Zubax/gridsens_gs2/firmware/src/air_sensor.cpp

/*
 * Copyright (C) 2014-2015  Zubax Robotics  <info@zubax.com>
 *
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
 * Author: Pavel Kirienko <pavel.kirienko@zubax.com>
 */

#include "air_sensor.hpp"
#include "node.hpp"
#include "board/ms5611.hpp"

#include <uavcan/equipment/air_data/StaticPressure.hpp>
#include <uavcan/equipment/air_data/StaticTemperature.hpp>

#include <ch.hpp>
#include <zubax_chibios/os.hpp>
#include <zubax_chibios/util/helpers.hpp>
#include <unistd.h>


namespace air_sensor
{
namespace
{

constexpr unsigned TemperaturePeriodRatio = 5;

const float OperatingTemperatureRange[] = {             ///< Operating temperature, defined by the specification
    -40 + ms5611::DegreesCelsiusToKelvinOffset,
    +80 + ms5611::DegreesCelsiusToKelvinOffset
};

const unsigned MinPublicationPeriodUSec = unsigned(1e6 / 40);

os::config::Param<unsigned> param_period_usec("uavcan.pubp-pres",
                                              0, 0, 1000000);

os::config::Param<unsigned> param_prio("uavcan.prio-pres",
                                       16,
                                       uavcan::TransferPriority::NumericallyMin,
                                       uavcan::TransferPriority::NumericallyMax);

os::config::Param<float> param_pressure_variance("pres.variance", 100.0, 1.0, 4000.0);
os::config::Param<float> param_temperature_variance("temp.variance", 4.0, 1.0, 100.0);

chibios_rt::Mutex last_sample_mutex;
Sample last_sample;


class AirSensorThread : public chibios_rt::BaseStaticThread<1024>
{
    float pressure_variance = 0;
    float temperature_variance = 0;

    mutable os::watchdog::Timer watchdog_;
    mutable ms5611::MS5611 driver_;

    static bool isInRange(float value, const float range_min_max[2])
    {
        return (value >= range_min_max[0]) && (value <= range_min_max[1]);
    }

    void publish(float pressure_pa, float temperature_k) const
    {
        {
            os::MutexLocker mlock(last_sample_mutex);
            last_sample.seq_id++;
            last_sample.pressure_pa = pressure_pa;
            last_sample.temperature_k = temperature_k;
        }

        if (!node::isStarted())
        {
            return;
        }

        static uavcan::equipment::air_data::StaticPressure pressure;
        pressure.static_pressure = pressure_pa;
        pressure.static_pressure_variance = pressure_variance;

        static uavcan::equipment::air_data::StaticTemperature temperature;
        temperature.static_temperature = temperature_k;
        temperature.static_temperature_variance = temperature_variance;

        node::Lock locker;
        auto& node = node::getNode();

        static uavcan::Publisher<uavcan::equipment::air_data::StaticPressure> pressure_pub(node);
        static uavcan::Publisher<uavcan::equipment::air_data::StaticTemperature> temperature_pub(node);

        EXECUTE_ONCE_NON_THREAD_SAFE
        {
            pressure_pub.setPriority(param_prio.get());
            temperature_pub.setPriority(param_prio.get());
        }

        (void)pressure_pub.broadcast(pressure);

        static unsigned temperature_publishing_frequency_divider = 0;
        temperature_publishing_frequency_divider++;
        if (temperature_publishing_frequency_divider >= TemperaturePeriodRatio)
        {
            temperature_publishing_frequency_divider = 0;
            (void)temperature_pub.broadcast(temperature);
        }
    }

    void tryRun() const
    {
        systime_t sleep_until = chibios_rt::System::getTime();

        assert(param_period_usec.get() > 0);
        const unsigned period_usec = std::max(MinPublicationPeriodUSec, param_period_usec.get());

        while (!os::isRebootRequested())
        {
            watchdog_.reset();
            sleep_until += US2ST(period_usec);

            const auto sample = driver_.read();
            if (!sample.first)
            {
                os::lowsyslog("Air sensor read failed\n");
                break;
            }

            publish(sample.second.pressure, sample.second.temperature);

            if (!isInRange(sample.second.temperature, OperatingTemperatureRange))
            {
                node::setComponentHealth(node::ComponentID::AirSensor, uavcan::protocol::NodeStatus::HEALTH_WARNING);
            }
            else
            {
                node::setComponentHealth(node::ComponentID::AirSensor, uavcan::protocol::NodeStatus::HEALTH_OK);
            }

            os::sleepUntilChTime(sleep_until);
        }
    }

public:
    AirSensorThread() :
        driver_(&SPID3, GPIO_PORT_BAROMETER_CHIP_SELECT, GPIO_PIN_BAROMETER_CHIP_SELECT)
    { }

    virtual ~AirSensorThread() { }

    void main() override
    {
        watchdog_.startMSec(1100);
        setName("air_sensor");

        pressure_variance = param_pressure_variance.get();
        temperature_variance = param_temperature_variance.get();

        while (!os::isRebootRequested())
        {
            watchdog_.reset();
            ::usleep(500000);
            watchdog_.reset();

            if (!driver_.init())
            {
                os::lowsyslog("Air sensor init failed, will retry...\n");
                continue;
            }

            os::lowsyslog("Air sensor init OK\n");

            node::markComponentInitialized(node::ComponentID::AirSensor);
            tryRun();
            if (!os::isRebootRequested())
            {
                node::setComponentHealth(node::ComponentID::AirSensor, uavcan::protocol::NodeStatus::HEALTH_ERROR);
                os::lowsyslog("Air sensor is about to restart...\n");
            }
        }

        os::lowsyslog("Air sensor driver terminated\n");
    }
} air_sensor_thread;

}

void init()
{
    if (param_period_usec.get() > 0)
    {
        (void)air_sensor_thread.start(HIGHPRIO - 10);
    }
    else
    {
        node::markComponentInitialized(node::ComponentID::AirSensor);
        os::lowsyslog("Air sensor disabled\n");
    }
}

Sample getLastSample()
{
    os::MutexLocker mlock(last_sample_mutex);
    return last_sample;
}

}
