Zubax/gridsens_gs2/firmware/src/sys/mcuconf.h

/*
 * STM32F107 drivers configuration.
 * The following settings override the default settings present in
 * the various device driver implementation headers.
 * Note that the settings for each driver only have effect if the whole
 * driver is enabled in halconf.h.
 *
 * IRQ priorities:
 * 15...0       Lowest...Highest.
 *
 * DMA priorities:
 * 0...3        Lowest...Highest.
 */

#define STM32F107_MCUCONF

#define STM32_ST_USE_TIMER                  5

/*
 * HAL driver system settings.
 */
#define STM32_NO_INIT                       FALSE
#define STM32_HSI_ENABLED                   TRUE  // Needed for FLASH programming
#define STM32_LSI_ENABLED                   TRUE  // Needed for watchdog
#define STM32_HSE_ENABLED                   TRUE
#define STM32_LSE_ENABLED                   FALSE
#define STM32_SW                            STM32_SW_PLL
#define STM32_PLLSRC                        STM32_PLLSRC_PREDIV1
#define STM32_PREDIV1SRC                    STM32_PREDIV1SRC_HSE
#define STM32_PREDIV1_VALUE                 2
#define STM32_PLLMUL_VALUE                  9
#define STM32_PREDIV2_VALUE                 4
#define STM32_PLL2MUL_VALUE                 16
#define STM32_PLL3MUL_VALUE                 16
#define STM32_HPRE                          STM32_HPRE_DIV1
#define STM32_PPRE1                         STM32_PPRE1_DIV2
#define STM32_PPRE2                         STM32_PPRE2_DIV2
#define STM32_ADCPRE                        STM32_ADCPRE_DIV4
#define STM32_OTG_CLOCK_REQUIRED            TRUE
#define STM32_OTGFSPRE                      STM32_OTGFSPRE_DIV3
#define STM32_I2S_CLOCK_REQUIRED            FALSE
#define STM32_MCOSEL                        STM32_MCOSEL_NOCLOCK
#define STM32_RTCSEL                        STM32_RTCSEL_HSEDIV
#define STM32_PVD_ENABLE                    FALSE
#define STM32_PLS                           STM32_PLS_LEV0

/*
 * ADC driver system settings.
 */
#define STM32_ADC_USE_ADC1                  FALSE
#define STM32_ADC_ADC1_DMA_PRIORITY         2
#define STM32_ADC_ADC1_IRQ_PRIORITY         6

/*
 * CAN driver system settings.
 */
#define STM32_CAN_USE_CAN1                  FALSE
#define STM32_CAN_USE_CAN2                  FALSE
#define STM32_CAN_CAN1_IRQ_PRIORITY         4
#define STM32_CAN_CAN2_IRQ_PRIORITY         4

/*
 * EXT driver system settings.
 */
#define STM32_EXT_EXTI0_IRQ_PRIORITY        6
#define STM32_EXT_EXTI1_IRQ_PRIORITY        6
#define STM32_EXT_EXTI2_IRQ_PRIORITY        6
#define STM32_EXT_EXTI3_IRQ_PRIORITY        6
#define STM32_EXT_EXTI4_IRQ_PRIORITY        6
#define STM32_EXT_EXTI5_9_IRQ_PRIORITY      6
#define STM32_EXT_EXTI10_15_IRQ_PRIORITY    6
#define STM32_EXT_EXTI16_IRQ_PRIORITY       6
#define STM32_EXT_EXTI17_IRQ_PRIORITY       6
#define STM32_EXT_EXTI18_IRQ_PRIORITY       6
#define STM32_EXT_EXTI19_IRQ_PRIORITY       6

/*
 * GPT driver system settings.
 */
#define STM32_GPT_USE_TIM1                  FALSE
#define STM32_GPT_USE_TIM2                  FALSE
#define STM32_GPT_USE_TIM3                  FALSE
#define STM32_GPT_USE_TIM4                  FALSE
#define STM32_GPT_USE_TIM5                  FALSE
#define STM32_GPT_USE_TIM8                  FALSE
#define STM32_GPT_TIM1_IRQ_PRIORITY         7
#define STM32_GPT_TIM2_IRQ_PRIORITY         7
#define STM32_GPT_TIM3_IRQ_PRIORITY         7
#define STM32_GPT_TIM4_IRQ_PRIORITY         7
#define STM32_GPT_TIM5_IRQ_PRIORITY         7
#define STM32_GPT_TIM8_IRQ_PRIORITY         7

/*
 * I2C driver system settings.
 * On IRQ priority levels: http://forum.chibios.org/phpbb/viewtopic.php?f=25&t=3085&p=23830
 */
#define STM32_I2C_USE_I2C1                  FALSE
#define STM32_I2C_USE_I2C2                  FALSE
#define STM32_I2C_I2C1_IRQ_PRIORITY         2
#define STM32_I2C_I2C2_IRQ_PRIORITY         2
#define STM32_I2C_I2C1_DMA_PRIORITY         3
#define STM32_I2C_I2C2_DMA_PRIORITY         3
#define STM32_I2C_DMA_ERROR_HOOK(i2cp)      osalSysHalt("DMA failure")

/*
 * ICU driver system settings.
 */
#define STM32_ICU_USE_TIM1                  FALSE
#define STM32_ICU_USE_TIM2                  FALSE
#define STM32_ICU_USE_TIM3                  FALSE
#define STM32_ICU_USE_TIM4                  FALSE
#define STM32_ICU_USE_TIM5                  FALSE
#define STM32_ICU_USE_TIM8                  FALSE
#define STM32_ICU_TIM1_IRQ_PRIORITY         7
#define STM32_ICU_TIM2_IRQ_PRIORITY         7
#define STM32_ICU_TIM3_IRQ_PRIORITY         7
#define STM32_ICU_TIM4_IRQ_PRIORITY         7
#define STM32_ICU_TIM5_IRQ_PRIORITY         7
#define STM32_ICU_TIM8_IRQ_PRIORITY         7

/*
 * PWM driver system settings.
 */
#define STM32_PWM_USE_ADVANCED              FALSE
#define STM32_PWM_USE_TIM1                  FALSE
#define STM32_PWM_USE_TIM2                  FALSE
#define STM32_PWM_USE_TIM3                  FALSE
#define STM32_PWM_USE_TIM4                  FALSE
#define STM32_PWM_USE_TIM5                  FALSE
#define STM32_PWM_USE_TIM8                  FALSE
#define STM32_PWM_TIM1_IRQ_PRIORITY         7
#define STM32_PWM_TIM2_IRQ_PRIORITY         7
#define STM32_PWM_TIM3_IRQ_PRIORITY         7
#define STM32_PWM_TIM4_IRQ_PRIORITY         7
#define STM32_PWM_TIM5_IRQ_PRIORITY         7
#define STM32_PWM_TIM8_IRQ_PRIORITY         7

/*
 * RTC driver system settings.
 */
#define STM32_RTC_IRQ_PRIORITY              15

/*
 * SERIAL driver system settings.
 */
#define STM32_SERIAL_USE_USART1             FALSE
#define STM32_SERIAL_USE_USART2             TRUE        // u-blox
#define STM32_SERIAL_USE_USART3             TRUE        // debug serial
#define STM32_SERIAL_USE_UART4              FALSE
#define STM32_SERIAL_USE_UART5              FALSE
#define STM32_SERIAL_USART1_PRIORITY        12
#define STM32_SERIAL_USART2_PRIORITY        12
#define STM32_SERIAL_USART3_PRIORITY        12
#define STM32_SERIAL_UART4_PRIORITY         12
#define STM32_SERIAL_UART5_PRIORITY         12

/*
 * SPI driver system settings.
 */
#define STM32_SPI_USE_SPI1                  FALSE
#define STM32_SPI_USE_SPI2                  FALSE
#define STM32_SPI_USE_SPI3                  TRUE
#define STM32_SPI_SPI1_DMA_PRIORITY         2
#define STM32_SPI_SPI2_DMA_PRIORITY         2
#define STM32_SPI_SPI3_DMA_PRIORITY         2
#define STM32_SPI_SPI1_IRQ_PRIORITY         3
#define STM32_SPI_SPI2_IRQ_PRIORITY         3
#define STM32_SPI_SPI3_IRQ_PRIORITY         3
#define STM32_SPI_DMA_ERROR_HOOK(spip)      osalSysHalt("DMA failure")

/*
 * UART driver system settings.
 */
#define STM32_UART_USE_USART1               FALSE
#define STM32_UART_USE_USART2               FALSE
#define STM32_UART_USE_USART3               FALSE
#define STM32_UART_USART1_IRQ_PRIORITY      12
#define STM32_UART_USART2_IRQ_PRIORITY      12
#define STM32_UART_USART3_IRQ_PRIORITY      12
#define STM32_UART_USART1_DMA_PRIORITY      0
#define STM32_UART_USART2_DMA_PRIORITY      0
#define STM32_UART_USART3_DMA_PRIORITY      0
#define STM32_UART_DMA_ERROR_HOOK(uartp)    osalSysHalt("DMA failure")

/*
 * USB driver system settings.
 */
#define STM32_USB_USE_OTG1                  TRUE
#define STM32_USB_OTG1_IRQ_PRIORITY         15
#define STM32_USB_OTG1_RX_FIFO_SIZE         512
#define STM32_USB_OTG_THREAD_PRIO           LOWPRIO
#define STM32_USB_OTG_THREAD_STACK_SIZE     200
#define STM32_USB_OTGFIFO_FILL_BASEPRI      0
