Zubax/gridsens_gs2/firmware/src/board/board.cpp

/*
 * Copyright (C) 2014-2015  Zubax Robotics  <info@zubax.com>
 *
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
 * Author: Pavel Kirienko <pavel.kirienko@zubax.com>
 */

#include "board.hpp"
#include <cstring>
#include <ch.hpp>
#include <hal.h>
#include <unistd.h>
#include <zubax_chibios/platform/stm32/flash_writer.hpp>
#include <zubax_chibios/platform/stm32/config_storage.hpp>

#if CORTEX_VTOR_INIT == 0
# error CORTEX_VTOR_INIT
#endif

/**
 * GPIO config for ChibiOS PAL driver
 */
const PALConfig pal_default_config =
{
    { VAL_GPIOAODR, VAL_GPIOACRL, VAL_GPIOACRH },
    { VAL_GPIOBODR, VAL_GPIOBCRL, VAL_GPIOBCRH },
    { VAL_GPIOCODR, VAL_GPIOCCRL, VAL_GPIOCCRH },
    { VAL_GPIODODR, VAL_GPIODCRL, VAL_GPIODCRH },
    { VAL_GPIOEODR, VAL_GPIOECRL, VAL_GPIOECRH }
};

/// Provided by linker
const extern std::uint8_t DeviceSignatureStorage[];

namespace board
{
/**
 * SPI is clocked from PCLK1 which is clocked at 36 MHz.
 */
static const SPIConfig SPICfg =
{
    nullptr,
    nullptr,
    0,
    SPI_CR1_BR_1 | SPI_CR1_BR_0
};

// This can't be constexpr because of reinterpret_cast<>
static void* const ConfigStorageAddress = reinterpret_cast<void*>(0x08000000 + (256 * 1024) - 1024);
constexpr unsigned ConfigStorageSize = 1024;


os::watchdog::Timer init(unsigned wdt_timeout_ms)
{
    /*
     * OS
     */
    halInit();
    chSysInit();
    sdStart(&STDOUT_SD, NULL);
    spiStart(&SPID3, &SPICfg);

    /*
     * Watchdog
     */
    os::watchdog::init();
    os::watchdog::Timer wdt;
    wdt.startMSec(wdt_timeout_ms);

    /*
     * Version check
     */
    const auto hw_ver = detectHardwareVersion();

    if (hw_ver.major != 2)
    {
        chibios_rt::System::halt("UNSUPPORTED HARDWARE: MAJOR VERSION");
    }

    if (hw_ver.minor != 2)
    {
        chibios_rt::System::halt("UNSUPPORTED HARDWARE: MINOR VERSION");
    }

    /*
     * Configuration manager
     */
    static os::stm32::ConfigStorageBackend config_storage_backend(ConfigStorageAddress, ConfigStorageSize);
    const int config_init_res = os::config::init(&config_storage_backend);
    if (config_init_res < 0)
    {
        die(config_init_res);
    }

    /*
     * Prompt
     */
    os::lowsyslog(PRODUCT_NAME_STRING " %d.%d %d.%d.%08x / %d %s\n",
                  hw_ver.major, hw_ver.minor,
                  FW_VERSION_MAJOR, FW_VERSION_MINOR, GIT_HASH, config_init_res,
                  watchdogTriggeredLastReset() ? "WDTRESET" : "OK");

    return wdt;
}

__attribute__((noreturn))
void die(int error)
{
    os::lowsyslog("Fatal error %i\n", error);
    while (1)
    {
        setStatusLed(false);
        ::usleep(25000);
        setStatusLed(true);
        ::usleep(25000);
    }
}

void setCANLed(unsigned iface_index, bool state)
{
    switch (iface_index)
    {
    case 0:
    {
        palWritePad(GPIO_PORT_LED_CAN1, GPIO_PIN_LED_CAN1, std::uint8_t(state));
        break;
    }
    case 1:
    {
        palWritePad(GPIO_PORT_LED_CAN2, GPIO_PIN_LED_CAN2, std::uint8_t(state));
        break;
    }
    default:
    {
        break;
    }
    }
}

void setStatusLed(bool state)
{
    palWritePad(GPIO_PORT_LED_STATUS, GPIO_PIN_LED_STATUS, std::uint8_t(state));
}

void restart()
{
    NVIC_SystemReset();
}

void readUniqueID(UniqueID& out_bytes)
{
    std::memcpy(out_bytes.data(), reinterpret_cast<const void*>(0x1FFFF7E8), std::tuple_size<UniqueID>::value);
}

bool tryReadDeviceSignature(DeviceSignature& out_sign)
{
    std::memcpy(out_sign.data(), &DeviceSignatureStorage[0], std::tuple_size<DeviceSignature>::value);

    bool valid = false;
    for (auto x : out_sign)
    {
        if (x != 0xFF && x != 0x00)          // All 0xFF/0x00 is not a valid signature, it's empty storage
        {
            valid = true;
            break;
        }
    }

    return valid;
}

bool tryWriteDeviceSignature(const DeviceSignature& sign)
{
    {
        DeviceSignature dummy;
        if (tryReadDeviceSignature(dummy))
        {
            return false;               // Already written
        }
    }

    // Before flash can be written, the source must be aligned.
    alignas(4) std::uint8_t aligned_buffer[std::tuple_size<DeviceSignature>::value];
    std::copy(std::begin(sign), std::end(sign), std::begin(aligned_buffer));

    os::stm32::FlashWriter writer;

    return writer.write(&DeviceSignatureStorage[0], &aligned_buffer[0], sizeof(aligned_buffer));
}

HardwareVersion detectHardwareVersion()
{
    auto v = HardwareVersion();

    v.major = HW_VERSION_MAJOR;

    if (palReadPad(GPIO_PORT_HWID, GPIO_PIN_HWID_BIT0))
    {
        v.minor += 1;
    }

    if (!palReadPad(GPIO_PORT_HWID, GPIO_PIN_HWID_BIT1_INVERSE))
    {
        v.minor += 2;
    }

    if (palReadPad(GPIO_PORT_HWID, GPIO_PIN_HWID_BIT2))
    {
        v.minor += 4;
    }

    return v;
}

}

/*
 * Early init from ChibiOS
 */
extern "C"
{

void __early_init(void)
{
    stm32_clock_init();
}

void boardInit(void)
{
    uint32_t mapr = AFIO->MAPR;
    mapr &= ~AFIO_MAPR_SWJ_CFG; // these bits are write-only

    // Enable SWJ only, JTAG is not needed at all:
    mapr |= AFIO_MAPR_SWJ_CFG_JTAGDISABLE;

    AFIO->MAPR = mapr | AFIO_MAPR_CAN_REMAP_REMAP2 | AFIO_MAPR_SPI3_REMAP;

    /*
     * Making sure the CAN controller is disabled!
     * The bootloader may or may not leave it enabled.
     * Let paranoia begin.
     */
    RCC->APB1RSTR |=  (RCC_APB1RSTR_CAN1RST | RCC_APB1RSTR_CAN2RST);
    RCC->APB1RSTR &= ~(RCC_APB1RSTR_CAN1RST | RCC_APB1RSTR_CAN2RST);

    CAN1->IER = CAN2->IER = 0;                                  // Disable interrupts
    CAN1->MCR = CAN2->MCR = CAN_MCR_SLEEP | CAN_MCR_RESET;      // Software reset

    NVIC_ClearPendingIRQ(CAN1_RX0_IRQn);
    NVIC_ClearPendingIRQ(CAN1_RX1_IRQn);
    NVIC_ClearPendingIRQ(CAN1_TX_IRQn);
    NVIC_ClearPendingIRQ(CAN1_SCE_IRQn);

    NVIC_ClearPendingIRQ(CAN2_RX0_IRQn);
    NVIC_ClearPendingIRQ(CAN2_RX1_IRQn);
    NVIC_ClearPendingIRQ(CAN2_TX_IRQn);
    NVIC_ClearPendingIRQ(CAN2_SCE_IRQn);
    // End of paranoia here.

    /*
     * Enabling the CAN controllers, then configuring GPIO functions for CAN_TX.
     * Order matters, otherwise the CAN_TX pins will twitch, disturbing the CAN bus.
     * This is why we can't perform this initialization using ChibiOS GPIO configuration.
     *
     * NOTE: Check this - the problem may only appear when CAN pin remapping is used,
     *       because ChibiOS initializes AFIO after GPIO.
     */
    RCC->APB1ENR |= RCC_APB1ENR_CAN1EN;
    palSetPadMode(GPIOB, 9, PAL_MODE_STM32_ALTERNATE_PUSHPULL);

#if UAVCAN_STM32_NUM_IFACES > 1
    RCC->APB1ENR |= RCC_APB1ENR_CAN2EN;
    palSetPadMode(GPIOB, 13, PAL_MODE_STM32_ALTERNATE_PUSHPULL);
#endif
}

}
