Zubax/gridsens_gs2/firmware/src/board/ublox.cpp

/*
 * Copyright (C) 2014-2017  Zubax Robotics  <info@zubax.com>
 *
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
 * Author: Pavel Kirienko <pavel.kirienko@zubax.com>
 */

#include "ublox.hpp"
#include <ctime>
#include <cstring>
#include <zubax_chibios/os.hpp>

namespace ublox
{
/*
 * MessageReceiver::ChecksumComputer
 */
void ChecksumComputer::add(std::uint8_t byte)
{
    checksum_a += byte;
    checksum_b += checksum_a;
}

void ChecksumComputer::add(const std::uint8_t* data, unsigned len)
{
    while (len --> 0)
    {
        add(*data++);
    }
}

/*
 * MessageReceiver
 */
constexpr std::uint8_t MessageReceiver::InvalidClassValues[];

bool MessageReceiver::nextByte(const Timestamps& ts, std::uint8_t byte)
{
    bool ret_value = false;

    //os::lowsyslog("%02x ", int(byte));

    switch (state)
    {
    case State::SyncChar1:
    {
        if (byte == 0xB5)
        {
            state = State::SyncChar2;
            sync_char_ts = ts;
        }
        break;
    }
    case State::SyncChar2:
    {
        state = (byte == 0x62) ? State::Class : State::SyncChar1;
        break;
    }
    case State::Class:
    {
        for (auto val : InvalidClassValues)
        {
            if (byte == val)
            {
                reset();
                break;
            }
        }
        cls = byte;
        state = State::ID;
        break;
    }
    case State::ID:
    {
        id = byte;
        state = State::Length1;
        break;
    }
    case State::Length1:
    {
        payload_len_expected = byte;
        state = State::Length2;
        break;
    }
    case State::Length2:
    {
        payload_len_expected |= static_cast<std::uint16_t>(byte) << 8;
        payload_len_received = 0;
        if (payload_len_expected <= payload_buffer_len)
        {
            state = State::Payload;
        }
        else
        {
            // The message is too long, likely invalid
            os::lowsyslog("ublox: Msg too long %d\n", int(payload_len_expected));
            reset();
        }
        break;
    }
    case State::Payload:
    {
        // Will not work wit zero-length payload
        payload_buffer[payload_len_received] = byte;
        payload_len_received++;
        if (payload_len_received >= payload_len_expected)
        {
            state = State::ChecksumA;
        }
        break;
    }
    case State::ChecksumA:
    {
        checksum_a = byte;
        state = State::ChecksumB;
        break;
    }
    case State::ChecksumB:
    {
        checksum_b = byte;
        state = State::SyncChar1;   // This message is now compelte, restart

        ChecksumComputer ckc;
        ckc.add(cls);
        ckc.add(id);
        ckc.add(payload_len_expected & 0xFF);
        ckc.add((payload_len_expected >> 8) & 0xFF);
        ckc.add(payload_buffer, payload_len_received);

        ret_value = (ckc.checksum_a == checksum_a) && (ckc.checksum_b == checksum_b);
        if (!ret_value)
        {
            os::lowsyslog("ublox: Invalid checksum\n");
        }
        break;
    }
    default:
    {
        assert(0);
        reset();
    }
    }

    return ret_value;
}

unsigned MessageReceiver::getReadLenHint() const
{
    unsigned retval = 1;
    if ((state == State::Payload) && (payload_len_expected > payload_len_received))
    {
        retval = payload_len_expected - payload_len_received;
    }
    assert(retval > 0);
    return retval;
}

RxMessage MessageReceiver::getReceivedMessage() const
{
    RxMessage msg{};
    msg.mono_usec = sync_char_ts.mono_usec;
    msg.real_usec = sync_char_ts.real_usec;
    msg.cls = cls;
    msg.id = id;
    msg.len = payload_len_received;
    msg.payload = payload_buffer;
    assert(msg.len > 0);
    assert(msg.mono_usec > 0);
    return msg;
}

void MessageReceiver::reset()
{
    state = State::SyncChar1;
}

/*
 * IOManager
 */
constexpr unsigned IOManager::ValidBaudRates[];

void IOManager::handleReceivedMessage(const RxMessage& raw_msg)
{
    //os::lowsyslog("ublox: Rx 0x%02x 0x%02x %d\n", int(raw_msg.cls), int(raw_msg.id), int(raw_msg.len));

    if (auto msg = raw_msg.tryCastTo<msg::ACK_ACK>())
    {
        //os::lowsyslog("ublox: ACK 0x%02x 0x%02x\n", int(msg->clsID), int(msg->msgID));
        last_ack_.cls = msg->clsID;
        last_ack_.id  = msg->msgID;
        return;
    }
    else if (auto msg = raw_msg.tryCastTo<msg::ACK_NAK>())
    {
        os::lowsyslog("ublox: NAK 0x%02x 0x%02x\n", int(msg->clsID), int(msg->msgID));
        return;
    }
    else
    {
        if (on_message)
        {
            on_message(raw_msg);
        }
    }
}

bool IOManager::configure(os::watchdog::Timer& wdt)
{
    auto prt_uart = msg::CFG_PRT_UART();
    prt_uart.portID = msg::CFG_PRT_UART::PortID::UART1;
    prt_uart.mode = msg::CFG_PRT_UART::Mode8N1;
    prt_uart.baudRate = TargetBaudRate;
    prt_uart.inProtoMask  = msg::CFG_PRT_UART::InProtoMask::inUbx | msg::CFG_PRT_UART::InProtoMask::inRtcm;
    prt_uart.outProtoMask = msg::CFG_PRT_UART::OutProtoMask::outUbx;

    bool baudrate_detected = false;
    for (unsigned baudrate : ValidBaudRates)
    {
        wdt.reset();
        const auto last_msg_ts = last_received_msg_.mono_usec;

        os::lowsyslog("ublox: Trying baudrate %u...\n", baudrate);
        rx_.reset();
        platform_.portSetBaudRate(baudrate);

        // Set the same baudrate, wait for any valid message in response
        prt_uart.baudRate = baudrate;
        if (sendAndWaitAck(Message::make(prt_uart)) || (last_received_msg_.mono_usec > last_msg_ts))
        {
            os::lowsyslog("ublox: Baudrate match %u\n", baudrate);
            baudrate_detected = true;
            break;
        }
    }

    if (!baudrate_detected)
    {
        os::lowsyslog("Failed to detect baudrate\n");
        return false;
    }

    wdt.reset();
    prt_uart.baudRate = TargetBaudRate;
    (void)sendAndWaitAck(Message::make(prt_uart));
    platform_.portSetBaudRate(TargetBaudRate);
    rx_.reset();

    return true;
}

void IOManager::spin(unsigned timeout_ms)
{
    const auto deadline = platform_.getMonotonicUSec() + timeout_ms * 1000ULL;
    do
    {
        /*
         * Read from the port
         */
        constexpr unsigned ReadTimeoutMs = 1;
        constexpr unsigned BufferSize = 16;
        std::uint8_t buffer[BufferSize];
        Timestamps read_ts;
        unsigned bytes_read = std::min(rx_.getReadLenHint(), BufferSize);
        bytes_read = platform_.portRead(buffer, bytes_read, ReadTimeoutMs);
        read_ts.real_usec = platform_.getRealUSec();
        read_ts.mono_usec = platform_.getMonotonicUSec();

        /*
         * Pass the data to the receiver state machine byte-by-byte
         */
        const std::uint8_t* byte_ptr = buffer;
        while (bytes_read --> 0)
        {
            if (rx_.nextByte(read_ts, *byte_ptr++))
            {
                last_received_msg_ = rx_.getReceivedMessage();
                handleReceivedMessage(last_received_msg_);
            }
        }
    }
    while (platform_.getMonotonicUSec() < deadline);
}

void IOManager::send(const Message& msg)
{
    ChecksumComputer ckc;
    ckc.add(msg.cls);
    ckc.add(msg.id);
    ckc.add(msg.len & 0xFF);
    ckc.add((msg.len >> 8) & 0xFF);
    ckc.add(msg.payload, msg.len);

    static const std::uint8_t Header[] = { 0xB5, 0x62 };

    const std::uint8_t class_id[] = { msg.cls, msg.id };
    const std::uint8_t length[] = { std::uint8_t(msg.len & 0xFF), std::uint8_t((msg.len >> 8) & 0xFF) };
    const std::uint8_t checksum[] = { ckc.checksum_a, ckc.checksum_b };

    platform_.portWrite(Header, 2);
    platform_.portWrite(class_id, 2);
    platform_.portWrite(length, 2);
    if (msg.len > 0)
    {
        assert(msg.payload != nullptr);
        platform_.portWrite(msg.payload, msg.len);
    }
    platform_.portWrite(checksum, 2);
}

bool IOManager::sendAndWaitAck(const Message& msg, unsigned ack_timeout_ms)
{
    const auto deadline = platform_.getMonotonicUSec() + ack_timeout_ms * 1000ULL;

    send(msg);

    last_ack_ = LastAck();
    assert((last_ack_.cls == 0) && (last_ack_.id == 0));

    while (platform_.getMonotonicUSec() < deadline)
    {
        spin(0);
        if ((last_ack_.cls == msg.cls) && (last_ack_.id == msg.id))
        {
            return true;
        }
    }
    return false;
}

/*
 * Driver
 */
void Driver::handlePVT(const Timestamps& ts, const msg::NAV_PVT& pvt)
{
    fix_.ts = ts;

    // Position
    fix_.lat = pvt.lat / 1e7;
    fix_.lon = pvt.lon / 1e7;
    fix_.height_wgs84 = pvt.height / 1e3F;
    fix_.height_amsl  = pvt.hMSL / 1e3F;

    // Velocity
    fix_.ned_velocity[0] = pvt.velN / 1e3F;
    fix_.ned_velocity[1] = pvt.velE / 1e3F;
    fix_.ned_velocity[2] = pvt.velD / 1e3F;

    // Heading of motion
    fix_.heading_of_motion = pvt.headMot * 1e-5F;

    // Uncertainties
    static const auto variance_1e3 = [](const std::uint32_t x) { return (x / 1e3F) * (x / 1e3F); };

    fix_.position_covariance[0] = variance_1e3(pvt.hAcc);
    fix_.position_covariance[4] = variance_1e3(pvt.hAcc);
    fix_.position_covariance[8] = variance_1e3(pvt.vAcc);

    fix_.velocity_covariance[0] = variance_1e3(pvt.sAcc);
    fix_.velocity_covariance[4] = fix_.velocity_covariance[0];
    fix_.velocity_covariance[8] = fix_.velocity_covariance[0];

    fix_.pdop = pvt.pDOP * 0.01F;

    // Fix mode
    switch (pvt.fixType)
    {
    case msg::NAV_PVT::FixType::Fix2D:
        fix_.mode = Fix::Mode::Fix2D;
        break;

    case msg::NAV_PVT::FixType::Fix3D:
    case msg::NAV_PVT::FixType::GnssAndDeadReckoning:
        fix_.mode = Fix::Mode::Fix3D;
        break;

    case msg::NAV_PVT::FixType::TimeOnly:
        fix_.mode = Fix::Mode::Time;
        break;

    case msg::NAV_PVT::FixType::DeadReckoning:
    case msg::NAV_PVT::FixType::NoFix:
    default:
        fix_.mode = Fix::Mode::None;
        break;
    }

    // Misc
    fix_.sats_used = pvt.numSV;
    if (pvt.flags & msg::NAV_PVT::FlagsMask::diffSoln)
    {
        fix_.flags |= Fix::Flags::DifferentialSolution;
    }

    // UTC validness flag
    static const auto UtcValidFlags = msg::NAV_PVT::ValidMask::validDate | msg::NAV_PVT::ValidMask::validTime;
    fix_.utc_valid = ((pvt.valid & UtcValidFlags) == UtcValidFlags) && (pvt.year > 1900) && (pvt.month > 0);

    // UTC timestamp computation
    if (fix_.utc_valid)
    {
        auto tm = std::tm();
        tm.tm_year = pvt.year - 1900;
        tm.tm_mon  = pvt.month - 1;
        tm.tm_mday = pvt.day;
        tm.tm_hour = pvt.hour;
        tm.tm_min  = pvt.min;
        tm.tm_sec  = pvt.sec;
        tm.tm_isdst = 0;

        std::int64_t signed_usec = static_cast<std::int64_t>(std::mktime(&tm)) * 1000000LL;
        signed_usec += pvt.nano / 1000;      // nano may be negative, hence the timestamp is signed
        fix_.utc_usec = signed_usec;
    }

    // Report update
    if (on_fix)
    {
        on_fix(fix_);
        fix_ = Fix();   // Reset the message
    }
}

void Driver::handleSOL(const Timestamps&, const msg::NAV_SOL& sol)
{
    fix_.ecef.position[0] = double(sol.ecefX) * 0.01;
    fix_.ecef.position[1] = double(sol.ecefY) * 0.01;
    fix_.ecef.position[2] = double(sol.ecefZ) * 0.01;

    fix_.ecef.velocity[0] = float(sol.ecefVX) * 0.01F;
    fix_.ecef.velocity[1] = float(sol.ecefVY) * 0.01F;
    fix_.ecef.velocity[2] = float(sol.ecefVZ) * 0.01F;

    static const auto variance_1e2 = [](const std::uint32_t x) { return (x / 1e2F) * (x / 1e2F); };

    std::fill_n(fix_.ecef.position_variance, 3, variance_1e2(sol.pAcc));
    std::fill_n(fix_.ecef.velocity_variance, 3, variance_1e2(sol.sAcc));
}

void Driver::handleDOP(const Timestamps& ts, const msg::NAV_DOP& dop)
{
    aux_.ts = ts;
    aux_.gdop = dop.gDOP * 0.01F;
    aux_.pdop = dop.pDOP * 0.01F;
    aux_.hdop = dop.hDOP * 0.01F;
    aux_.vdop = dop.vDOP * 0.01F;
    aux_.tdop = dop.tDOP * 0.01F;
    aux_.ndop = dop.nDOP * 0.01F;
    aux_.edop = dop.eDOP * 0.01F;

    if (on_aux)
    {
        on_aux(aux_);
    }
}

void Driver::handleSAT(const Timestamps& ts, const msg::NAV_SAT& sat)
{
    (void)ts;
    if (sat.version != msg::NAV_SAT::MsgVersion)
    {
        os::lowsyslog("ublox: NAV-SAT of unsupported version %i\n", int(sat.version));
        return;
    }

    aux_.num_sats = sat.numSvs;

    for (unsigned i = 0; i < std::min(static_cast<unsigned>(sat.numSvs), Auxiliary::MaxSats); i++)
    {
        const auto src = sat.svs[i];
        auto& dst = aux_.sats[i];

        dst.gnss_id = src.gnssId;
        dst.sat_id = src.svId;
        dst.elevation = src.elev;
        dst.azimuth = src.azim;
        dst.signal_noise_ratio = src.cno;
        dst.used = (src.flags & msg::NAV_SAT::Sv::FlagsMask::svUsed) != 0;
    }
}

void Driver::handleTIMEGPS(const Timestamps& ts, const msg::NAV_TIMEGPS& timegps)
{
    leaps_ = GpsLeapSeconds();
    leaps_.ts = ts;

    if (timegps.valid & msg::NAV_TIMEGPS::ValidMask::leapSValid)
    {
        leaps_.num_leap_seconds = timegps.leapS;

        if (on_gps_leap_seconds)
        {
            on_gps_leap_seconds(leaps_);
        }
    }
}

void Driver::handleReceivedMessage(const RxMessage& raw_msg)
{
    if (auto msg = raw_msg.tryCastTo<msg::NAV_PVT>())
    {
        handlePVT(raw_msg, *msg);
    }
    else if (auto msg = raw_msg.tryCastTo<msg::NAV_SOL>())
    {
        handleSOL(raw_msg, *msg);
    }
    else if (auto msg = raw_msg.tryCastTo<msg::NAV_DOP>())
    {
        handleDOP(raw_msg, *msg);
    }
    else if (auto msg = raw_msg.tryCastTo<msg::NAV_SAT>())
    {
        handleSAT(raw_msg, *msg);
    }
    else if (auto msg = raw_msg.tryCastTo<msg::NAV_TIMEGPS>())
    {
        handleTIMEGPS(raw_msg, *msg);
    }
    else
    {
        os::lowsyslog("ublox: Unknown message: class=0x%02x id=0x%02x payload_len=%d\n",
                  int(raw_msg.cls), int(raw_msg.id), int(raw_msg.len));
    }
}

void Driver::logCfgGnssMessage(const msg::CFG_GNSS& msg)
{
    os::lowsyslog("ublox: CFG-GNSS numTrkChHw  = %u\n", unsigned(msg.numTrkChHw));
    os::lowsyslog("ublox: CFG-GNSS numTrkChUse = %u\n", unsigned(msg.numTrkChUse));

    for (unsigned i = 0; i < msg.numConfigBlocks; i++)
    {
        const msg::CFG_GNSS::ConfigBlock& b = msg.configBlocks[i];
        os::lowsyslog("ublox: CFG-GNSS block %u: gnssId=%u[%-7s] resTrkCh=%-2u maxTrkCh=%-2u flags=0x%08x[%s]\n",
                      i,
                      unsigned(b.gnssId),
                      msg::gnssIDToString(b.gnssId),
                      unsigned(b.resTrkCh),
                      unsigned(b.maxTrkCh),
                      unsigned(b.flags),
                      (b.flags & 1) ? "on" : "off");
    }
}

bool Driver::detectReceiver()
{
    auto mon_ver = io_.pollWithLength<msg::MON_VER>();
    if (mon_ver.first == nullptr)
    {
        os::lowsyslog("ublox: Failed to poll MON-VER\n");
        return false;
    }

    const unsigned num_extensions =
        (mon_ver.second - sizeof(msg::MON_VER::swVersion) - sizeof(msg::MON_VER::hwVersion)) /
        sizeof(msg::MON_VER::extension);

    static const auto as_string = [](auto s) {
        s[s.size() - 1] = '\0';
        return reinterpret_cast<const char*>(s.data());
    };

    os::lowsyslog("ublox: MON-VER: SW='%s' HW='%s'\n",
                  as_string(mon_ver.first->swVersion),
                  as_string(mon_ver.first->hwVersion));
    for (unsigned i = 0; i < num_extensions; i++)
    {
        os::lowsyslog("ublox: MON-VER extension %u: '%s'\n",
                      i,
                      as_string(mon_ver.first->extension[i]));
    }

    static const auto parse_uint = [](const char* begin, const char* end) -> std::pair<std::uint8_t, bool> {
        std::uint8_t out = 0;
        while (begin < end)
        {
            if (*begin < '0' || *begin > '9')
            {
                return {0, false};
            }
            out *= 10;
            out += *begin - '0';
            ++begin;
        }
        return {out, true};
    };

    // Parsing the response here
    for (unsigned i = 0; i < num_extensions; i++)
    {
        const char ProtocolVersionPrefix[] = "PROTVER=";
        const auto& current = mon_ver.first->extension[i];

        if (0 == std::strncmp(current.data(), &ProtocolVersionPrefix[0], sizeof(ProtocolVersionPrefix) - 1))
        {
            const char* const major_begin = &current[sizeof(ProtocolVersionPrefix) - 1];
            const char* const major_end   = static_cast<const char*>(std::memchr(major_begin, '.', 3));
            const char* const minor_begin = major_end + 1;
            const char* const minor_end   = static_cast<const char*>(std::memchr(minor_begin, '\0', 3));

            if ((major_begin == nullptr) ||
                (major_end   == nullptr) ||
                (minor_begin == nullptr) ||
                (minor_end   == nullptr) ||
                (major_end - major_begin > 2) ||
                (minor_end - minor_begin > 2) ||
                (major_end <= major_begin) ||
                (minor_end <= minor_begin))
            {
                os::lowsyslog("ublox: MON-VER: Invalid PROTVER string\n");
                return false;
            }

            const auto parse_output_major = parse_uint(major_begin, major_end);
            const auto parse_output_minor = parse_uint(minor_begin, minor_end);
            if (!parse_output_major.second ||
                !parse_output_minor.second)
            {
                os::lowsyslog("ublox: MON-VER: Could not parse protocol version\n");
                return false;
            }

            protocol_version_.major = parse_output_major.first;
            protocol_version_.minor = parse_output_minor.first;

            break;
        }
    }

    if (protocol_version_.major == 0)
    {
        os::lowsyslog("ublox: MON-VER: Could not detect protocol version\n");
        return false;
    }

    os::lowsyslog("ublox: Detected protocol version: %03d.%03d\n",
                  int(protocol_version_.major),
                  int(protocol_version_.minor));

    return true;
}

bool Driver::configureMessageRate(std::uint8_t cls, std::uint8_t id, std::uint8_t rate)
{
    msg::CFG_MSG msg;
    msg.msgClass = cls;
    msg.msgID    = id;
    msg.rate     = rate;
    return io_.sendAndWaitAck(Message::make(msg));
}

bool Driver::configureGnss(os::watchdog::Timer& wdt)
{
    // Nav rate
    wdt.reset();
    {
        float meas_rate = 1000.F / cfg_.fix_rate_hz;
        meas_rate = std::max(meas_rate, 1.F);
        meas_rate = std::min(meas_rate, 65534.F);

        auto rate = io_.allocateMessage<msg::CFG_RATE>();
        rate->measRate = static_cast<std::uint16_t>(meas_rate);
        rate->navRate = 1;                           // Required by the spec
        rate->timeRef = msg::CFG_RATE::TimeRef::UTC;
        if (!io_.sendAndWaitAck(Message::make(*rate)))
        {
            os::lowsyslog("ublox: CFG-RATE failed\n");
            return false;
        }
    }

    // GNSS configuration - only if the protocol version is above 18
    if (protocol_version_ >= UbloxProtocolVersion{18, 0})
    {
        auto cfg_gnss_ptr = io_.poll<msg::CFG_GNSS>();
        if (cfg_gnss_ptr == nullptr)
        {
            os::lowsyslog("ublox: Failed to poll CFG-GNSS\n");
            return false;
        }

        if (cfg_gnss_ptr->msgVer == msg::CFG_GNSS::MsgVersion)
        {
            os::lowsyslog("ublox: CFG-GNSS BEFORE configuration:\n");
            logCfgGnssMessage(*cfg_gnss_ptr);

            // Observe that the fields resTrkCh and maxTrkCh will become read-only starting from the protocol version 23
            // The values that we set are defaults, as reported by a ublox-M8Q protocol version 18
            msg::CFG_GNSS set = *cfg_gnss_ptr;
            set.numTrkChUse = cfg_gnss_ptr->numTrkChHw;
            set.numConfigBlocks = 7;

            // GPS is always enabled
            set.configBlocks[0].gnssId = msg::GnssID::GPS;
            set.configBlocks[0].resTrkCh = 8;
            set.configBlocks[0].maxTrkCh = 16;
            set.configBlocks[0].flags = (1U << 16) | 1;

            // Galileo is always enabled
            set.configBlocks[1].gnssId = msg::GnssID::Galileo;
            set.configBlocks[1].resTrkCh = 4;
            set.configBlocks[1].maxTrkCh = 8;
            set.configBlocks[1].flags = (1U << 16) | 1;

            // Beidou is always disabled. Switching between GNSS can be dangerous, see the section 4.2.1
            // BeiDou cannot be used concurrently with GLONASS on u-blox M8. We prefer GLONASS because it significantly
            // outperforms BeiDou in Europe, and probably in the rest of the world barring probably Asia.
            set.configBlocks[2].gnssId = msg::GnssID::BeiDou;
            set.configBlocks[2].resTrkCh = 8;
            set.configBlocks[2].maxTrkCh = 16;
            set.configBlocks[2].flags = (1U << 16) | 0;

            // GLONASS is always enabled
            set.configBlocks[3].gnssId = msg::GnssID::GLONASS;
            set.configBlocks[3].resTrkCh = 8;
            set.configBlocks[3].maxTrkCh = 14;
            set.configBlocks[3].flags = (1U << 16) | 1;         // Enabled always

            // QZSS must be enabled/disabled together with GPS (see the user manual)
            // L1-SAIF is disabled by default, but we turn it on here
            set.configBlocks[4].gnssId = msg::GnssID::QZSS;
            set.configBlocks[4].resTrkCh = 0;
            set.configBlocks[4].maxTrkCh = 3;
            set.configBlocks[4].flags = (4U << 16) | (1U << 16) | 1;

            // SBAS is always enabled, like GPS
            set.configBlocks[5].gnssId = msg::GnssID::SBAS;
            set.configBlocks[5].resTrkCh = 1;
            set.configBlocks[5].maxTrkCh = 3;
            set.configBlocks[5].flags = (1U << 16) | 1;

            // IMES is always disabled
            set.configBlocks[6].gnssId = msg::GnssID::IMES;
            set.configBlocks[6].resTrkCh = 0;
            set.configBlocks[6].maxTrkCh = 8;
            set.configBlocks[6].flags = (1U << 16) | 0;

            os::lowsyslog("ublox: Setting new CFG-GNSS...\n");
            if (!io_.sendAndWaitAck(Message::make(set, set.computeLength())))
            {
                os::lowsyslog("ublox: CFG-GNSS set failed\n");
                return false;
            }
            os::lowsyslog("ublox: New CFG-GNSS configuration has been confirmed by the receiver\n");

            cfg_gnss_ptr = io_.poll<msg::CFG_GNSS>();
            if (cfg_gnss_ptr == nullptr)
            {
                os::lowsyslog("ublox: Failed to poll CFG-GNSS\n");
                return false;
            }

            os::lowsyslog("ublox: CFG-GNSS AFTER configuration:\n");
            logCfgGnssMessage(*cfg_gnss_ptr);
        }
        else
        {
            os::lowsyslog("ublox: GNSS configuration skipped - unknown version of CFG-GNSS: %d\n",
                          int(cfg_gnss_ptr->msgVer));
        }
    }
    else
    {
        os::lowsyslog("ublox: GNSS configuration skipped - old protocol\n");
    }

    // GNSS configuration display
    wdt.reset();
    {
        msg::MON_GNSS mon_gnss;
        {
            auto mon_gnss_ptr = io_.poll<msg::MON_GNSS>();
            if (mon_gnss_ptr == nullptr)
            {
                os::lowsyslog("ublox: Failed to poll MON-GNSS\n");
                return false;
            }
            mon_gnss = *mon_gnss_ptr;
        }
        os::lowsyslog("ublox: MON-GNSS supported=%u default=%u enabled=%u simultaneous=%u\n",
                  unsigned(mon_gnss.supported), unsigned(mon_gnss.default_),
                  unsigned(mon_gnss.enabled), unsigned(mon_gnss.simultaneous));
    }

    // NAV5
    wdt.reset();
    {
        auto nav5 = io_.allocateMessage<msg::CFG_NAV5>();
        nav5->mask = msg::CFG_NAV5::Mask::dyn;

        switch (cfg_.dynamic_model)
        {
        case Config::DynamicModel::Automotive:
        {
            nav5->dynModel = msg::CFG_NAV5::DynModel::Automotive;
            break;
        }
        case Config::DynamicModel::Sea:
        {
            nav5->dynModel = msg::CFG_NAV5::DynModel::Sea;
            break;
        }
        case Config::DynamicModel::Airborne:
        {
            nav5->dynModel = msg::CFG_NAV5::DynModel::Airborne_4g;
            break;
        }
        default:
        {
            assert(false);
            nav5->dynModel = msg::CFG_NAV5::DynModel::Airborne_4g;      // The default
            break;
        }
        }
        os::lowsyslog("ublox: Dynamic model: 0x%02x\n", int(nav5->dynModel));

        if (!io_.sendAndWaitAck(Message::make(*nav5)))
        {
            os::lowsyslog("ublox: CFG-NAV5 failed\n");
            return false;
        }
    }

    return true;
}

bool Driver::configureMessages()
{
    if (!configureMessageRate(msg::NAV_PVT::Class, msg::NAV_PVT::ID, 1))  // Position-Velocity-Time solution
    {
        return false;
    }
    if (!configureMessageRate(msg::NAV_SOL::Class, msg::NAV_SOL::ID, 1))  // ECEF frame solution
    {
        return false;
    }
    if (!configureMessageRate(msg::NAV_TIMEGPS::Class, msg::NAV_TIMEGPS::ID, 1))
    {
        return false;
    }
    {
        unsigned dop_rate = (cfg_.fix_rate_hz / cfg_.aux_rate_hz + 0.5F);
        dop_rate = std::min(0xFFU, dop_rate);
        dop_rate = std::max(1U, dop_rate);
        if (!configureMessageRate(msg::NAV_DOP::Class, msg::NAV_DOP::ID, dop_rate))  // DOP values
        {
            return false;
        }
    }
    {
        unsigned sat_rate = (cfg_.fix_rate_hz / std::min(cfg_.aux_rate_hz, 1.0F) + 0.5F);
        sat_rate = std::min(0xFFU, sat_rate);
        sat_rate = std::max(1U, sat_rate);
        if (!configureMessageRate(msg::NAV_SAT::Class, msg::NAV_SAT::ID, sat_rate)) // Sat info
        {
            return false;
        }
    }
    return true;
}

bool Driver::configure(const Config& cfg, os::watchdog::Timer& wdt)
{
    wdt.reset();
    if (!io_.on_message)
    {
        io_.on_message = std::bind(&Driver::handleReceivedMessage, this, std::placeholders::_1);
    }

    cfg_ = cfg;
    cfg_.fix_rate_hz = std::max(cfg_.fix_rate_hz, 0.5F);
    cfg_.aux_rate_hz = std::max(cfg_.aux_rate_hz, 0.1F);
    cfg_.aux_rate_hz = std::min(cfg_.aux_rate_hz, cfg_.fix_rate_hz);

    wdt.reset();
    if (!io_.configure(wdt))
    {
        return false;
    }

    wdt.reset();
    if (!detectReceiver())
    {
        return false;
    }

    wdt.reset();
    if (!configureGnss(wdt))
    {
        return false;
    }

    wdt.reset();
    if (!configureMessages())
    {
        return false;
    }

    configured_at_mono_usec_ = io_.getMonotonicUSec();

    wdt.reset();
    return true;
}

void Driver::spin(unsigned timeout_ms)
{
    io_.spin(timeout_ms);
}

bool Driver::areRatesValid() const
{
    constexpr unsigned IntervalMultiplier = 3;
    const auto ts_mono_usec = io_.getMonotonicUSec();

    static const auto validate = [=](const Timestamps& ts, float expected_rate)
    {
        const auto max_interval_usec = static_cast<std::uint64_t>(1e6 / expected_rate + 0.5F) * IntervalMultiplier;
        if (ts_mono_usec > max_interval_usec)
        {
            const auto mono_usec = std::max(configured_at_mono_usec_, ts.mono_usec);
            if (mono_usec < (ts_mono_usec - max_interval_usec))
            {
                return false;
            }
        }
        return true;
    };

    return validate(getFix().ts, cfg_.fix_rate_hz) && validate(getAuxiliary().ts, cfg_.aux_rate_hz);
}

}
