Zubax/gridsens_gs2/firmware/src/uavcan.cpp

/*
 * Copyright (c) 2014 Courierdrone, courierdrone.com
 * Distributed under the MIT License, available in the file LICENSE.
 * Author: Pavel Kirienko <pavel.kirienko@courierdrone.com>
 */

#include <unistd.h>
#include <ch.hpp>

#include <crdr_chibios/config/config.hpp>
#include <crdr_chibios/sys/sys.h>

#include "uavcan.hpp"

namespace app
{
namespace
{

crdr_chibios::config::Param<unsigned> can_bitrate("can_bitrate", 1000000, 20000, 1000000);
crdr_chibios::config::Param<unsigned> node_id("uavcan_node_id", 42, 1, 120);

uavcan_stm32::CanInitHelper<> can;

uavcan_stm32::Mutex node_mutex;

void configureNode()
{
    UavcanNode& node = getUavcanNode();

    node.setNodeID(node_id.get());
    node.setName("com.courierdrone.gps");

    uavcan::protocol::SoftwareVersion swver;
    swver.major = FW_VERSION_MAJOR;
    swver.minor = FW_VERSION_MINOR;
    node.setSoftwareVersion(swver);

    uavcan::protocol::HardwareVersion hwver;
    hwver.major = HW_VERSION;
    node.setHardwareVersion(hwver);
}

/*
 * UAVCAN spin loop
 */
class : public chibios_rt::BaseStaticThread<3000>
{
public:
    msg_t main() override
    {
        configureNode();

        /*
         * Starting the UAVCAN node - this may take a few seconds
         */
        while (true)
        {
            {
                UavcanLock locker;
                const int uavcan_start_res = getUavcanNode().start();
                if (uavcan_start_res >= 0)
                {
                    break;
                }
                lowsyslog("Node initialization failure: %i, will try agin soon\n", uavcan_start_res);
            }
            ::sleep(3);
        }
        getUavcanNode().setStatusOk();

        /*
         * Main loop
         */
        lowsyslog("UAVCAN node started\n");
        while (true)
        {
            {
                UavcanLock locker;
                const int spin_res = getUavcanNode().spin(uavcan::MonotonicDuration::fromUSec(500));
                if (spin_res < 0)
                {
                    lowsyslog("UAVCAN spin failure: %i\n", spin_res);
                }
            }
            ::usleep(1000);
        }
        return msg_t();
    }
} node_thread;

}

UavcanLock::UavcanLock() : uavcan_stm32::MutexLocker(node_mutex) { }

bool isUavcanNodeStarted()
{
    return getUavcanNode().isStarted();
}

UavcanNode& getUavcanNode()
{
    static UavcanNode node(can.driver, uavcan_stm32::SystemClock::instance());
    return node;
}

int uavcanInit()
{
    const int can_res = can.init(can_bitrate.get());
    if (can_res < 0)
    {
        return can_res;
    }

    (void)node_thread.start(LOWPRIO);
    return 0;
}

}
