Zubax/gridsens_gs2/firmware/src/uavcan.hpp

/*
 * Copyright (c) 2014 Courierdrone, courierdrone.com
 * Distributed under the MIT License, available in the file LICENSE.
 * Author: Pavel Kirienko <pavel.kirienko@courierdrone.com>
 */

#pragma once

#include <uavcan_stm32/uavcan_stm32.hpp>

namespace app
{

struct UavcanLock : uavcan_stm32::MutexLocker
{
    UavcanLock();
};

typedef uavcan::Node<UAVCAN_MEM_POOL_BLOCK_SIZE * 64> UavcanNode;

bool isUavcanNodeStarted();

UavcanNode& getUavcanNode();

int uavcanInit();

}
